jeongm-in/touchpad-adventure/KiCad/framework-touchpad/framework-touchpad.kicad_sch

## KiCad design KiCad/framework-touchpad/framework-touchpad.kicad_sch (2024-12-30)

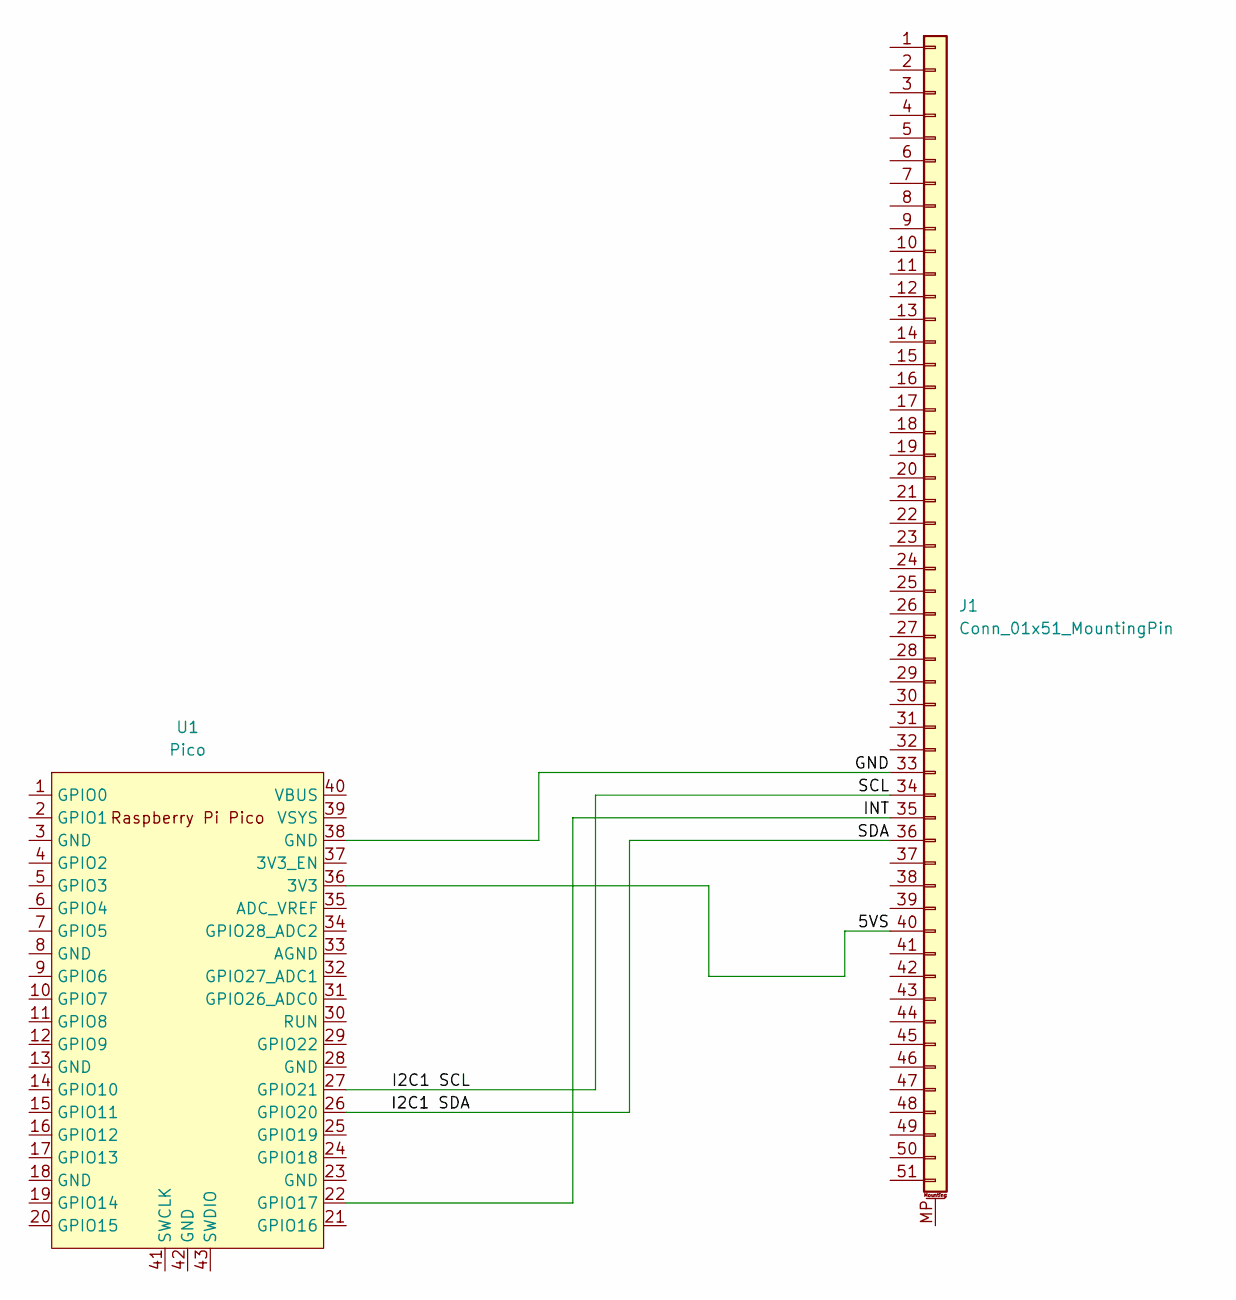
[picture p13: schematic framework-touchpad.kicad_sch]

Parts:
J1: Conn_01x51_MountingPin; FPC_51_0.5
U1: Pico; RPi_Pico_SMD_TH

Connections:
5VS: J1.40, U1.36 (3V3)
GND: J1.33, U1.38 (GND)
I2C1 SCL: J1.34, U1.27 (GPIO21)
I2C1 SDA: J1.36, U1.26 (GPIO20)
INT: J1.35, U1.22 (GPIO17)
